smartboxchannel/EFEKTA-EINK213-TEMP-HUM-PRESS-SENSOR-NRF52840-V2/CODE/Arduino/New_Version/imagedata.cpp

#include "imagedata.h"
#include <avr/pgmspace.h>


const unsigned char Especially[] PROGMEM =  { /* 0X01,0X01,0XB4,0X00,0X69,0X00, */
0X00,0X00,0X00,0X00,0X00,0X00,0X00,0X00,0X00,0X00,0X00,0X00,0X00,0X00,0X00,0X00,
0X00,0X00,0X00,0X00,0X00,0X00,0X00,0X00,0X00,0X00,0X00,0X00,0X00,0X00,0X00,0X00,
0X00,0X00,0X00,0X00,0X00,0X01,0XFC,0X00,0X00,0X00,0X00,0X00,0X00,0X00,0X00,0X00,
0X00,0X00,0X00,0X01,0X04,0X00,0X00,0X00,0X00,0X00,0X3F,0XFF,0XC0,0X00,0X00,0X00,
0X00,0X01,0X04,0X00,0X00,0X00,0X00,0X00,0X3F,0XFF,0XC0,0X00,0X00,0X00,0X00,0X01,
0X04,0X00,0X00,0X00,0X00,0X00,0X30,0X60,0XC0,0X00,0X00,0X00,0X00,0X01,0X04,0X00,
0X00,0X00,0X00,0X00,0X30,0X60,0XC0,0X00,0X00,0X00,0X00,0X01,0X04,0X07,0XF0,0X00,
0X00,0X00,0X30,0X60,0XC0,0X00,0X00,0X00,0X00,0X00,0XF8,0X04,0X40,0X00,0X00,0X00,
0X30,0X60,0XC0,0X00,0X00,0X00,0X00,0X00,0X00,0X04,0X40,0X00,0X00,0X00,0X30,0X60,
0XC0,0X00,0X00,0X00,0X00,0X00,0X00,0X04,0X40,0X00,0X00,0X00,0X30,0X60,0XC0,0X00,
0X00,0X00,0X00,0X00,0XF8,0X04,0X40,0X00,0X00,0X00,0X30,0X60,0XC0,0X00,0X00,0X00,
0X00,0X01,0X04,0X04,0X40,0X00,0X00,0X00,0X30,0X60,0XC0,0X00,0X00,0X00,0X00,0X01,
0X04,0X03,0X80,0X00,0X00,0X00,0X30,0X60,0XC0,0X00,0X00,0X00,0X00,0X01,0X04,0X00,
0X00,0X00,0X00,0X00,0X30,0X60,0XC0,0X00,0X00,0X00,0X00,0X01,0X04,0X00,0X00,0X00,
0X00,0X00,0X30,0X60,0XC0,0X00,0X00,0X00,0X00,0X01,0X04,0X00,0X00,0X00,0X00,0X00,
0X30,0X60,0XC0,0X00,0X00,0X00,0X00,0X00,0XF8,0X03,0XF0,0X00,0X00,0X00,0X30,0X00,
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
0XF8,0X7F,0XFF,0X80,0XF9,0XFF,0XFE,0X00,0XE7,0XFF,0XF0,0X00,0XFF,0XFF,0XC0,0X00,
0X7F,0XFF,0X00,0X00,0X3F,0XF8,0X00,0X00,0X1F,0XE0,0X00,0X00,0X0F,0X00,0X00,0X00,
0X00,0X00,0X00,0X00,0X00,0X00,0X00,0X00,0X00,0X00,0X00,0X00,};
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
