smartboxchannel/EFEKTA-EINK213-TEMP-HUM-PRESS-SENSOR-NRF52840-V2/CODE/Arduino/New_Version/imagedata.h

extern const unsigned char Especially[];
extern const unsigned char IMAGE_LOGO0[];
extern const unsigned char IMAGE_LOGO1[];
extern const unsigned char IMAGE_LOGO2[];
extern const unsigned char IMAGE_LOGO3[];
extern const unsigned char IMAGE_LOGO4[];
extern const unsigned char IMAGE_LOGO5[];
extern const unsigned char IMAGE_LOGO6[];
extern const unsigned char IMAGE_DATANL0[610];
extern const unsigned char IMAGE_DATANL00[624];
extern const unsigned char IMAGE_DATANL[608];
extern const unsigned char IMAGE_DATANL2[1160];
extern const unsigned char IMAGE_DATANL3[316];
extern const unsigned char IMAGE_DATANL4[790];
extern const unsigned char IMAGE_DATA_B100[];
extern const unsigned char IMAGE_DATA_B87[];
extern const unsigned char IMAGE_DATA_B75[];
extern const unsigned char IMAGE_DATA_B63[];
extern const unsigned char IMAGE_DATA_B50[];
extern const unsigned char IMAGE_DATA_B38[];
extern const unsigned char IMAGE_DATA_B25[];
extern const unsigned char IMAGE_DATA_B13[];
extern const unsigned char IMAGE_DATA_B0[];
extern const unsigned char IMAGE_DATA_L100[];
extern const unsigned char IMAGE_DATA_L80[];
extern const unsigned char IMAGE_DATA_L60[];
extern const unsigned char IMAGE_DATA_L40[];
extern const unsigned char IMAGE_DATA_L20[];
extern const unsigned char IMAGE_DATA_L0[];
extern const unsigned char IMAGE_DATA_W0[];
extern const unsigned char IMAGE_DATA_W1[];
extern const unsigned char IMAGE_DATA_W2[];
extern const unsigned char IMAGE_DATA_W3[];
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

extern const unsigned char IMAGE_CONF[648];
extern const unsigned char IMAGE_ECONF[648];
extern const unsigned char IMAGE_SEARCH[648];
extern const unsigned char IMAGE_ESEARCH[648];

extern const unsigned char IMAGE_RTIME[648];
extern const unsigned char IMAGE_ERTIME[648];

extern const unsigned char IMAGE_PAIR[648];
extern const unsigned char IMAGE_EPAIR[648];

extern const unsigned char IMAGE_RESET[648];
extern const unsigned char IMAGE_ERESET[648];

extern const unsigned char IMAGE_PRESENT[648];
extern const unsigned char IMAGE_EPRESENT[648];

extern const unsigned char IMAGE_ACTIV[216];
extern const unsigned char IMAGE_EACTIV[216];

extern const unsigned char IMAGE_UP[];
extern const unsigned char IMAGE_DOWN[];

extern const unsigned char IMAGE_COLOR[];
extern const unsigned char IMAGE_ECOLOR[];

extern const unsigned char IMAGE_CONACTIV[];
extern const unsigned char IMAGE_ECONACTIV[];
extern const unsigned char IMAGE_NOCONACTIV[];
extern const unsigned char IMAGE_ENOCONACTIV[];

/* FILE END */
